TheDany4545/Tesis-2022-Erick-Aquino/Estimulador/Caracterizacion/Gráficas/frec_rampa_20.png

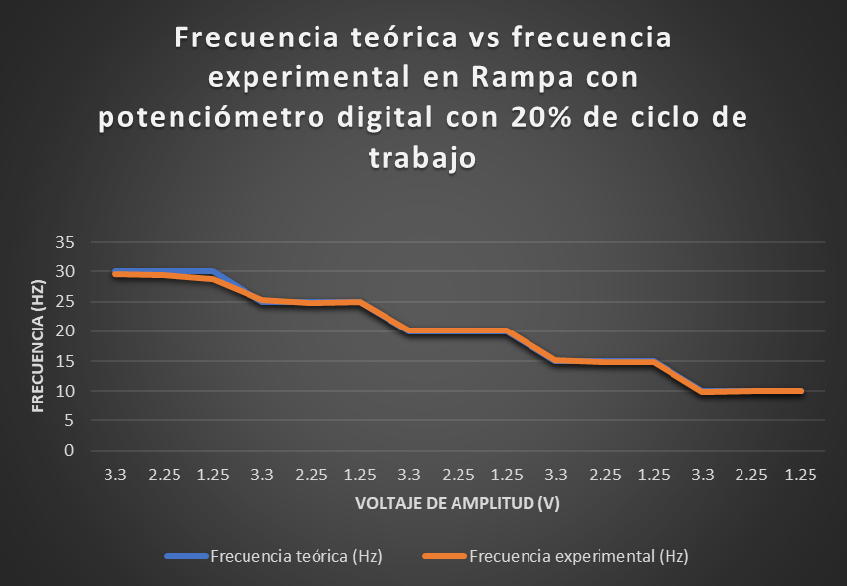
Estimulador/Caracterizacion/Gráficas/frec_rampa_20.png
