TheDany4545/Tesis-2022-Erick-Aquino/Documentación/Scheamtics/trinketM0_2.jpg

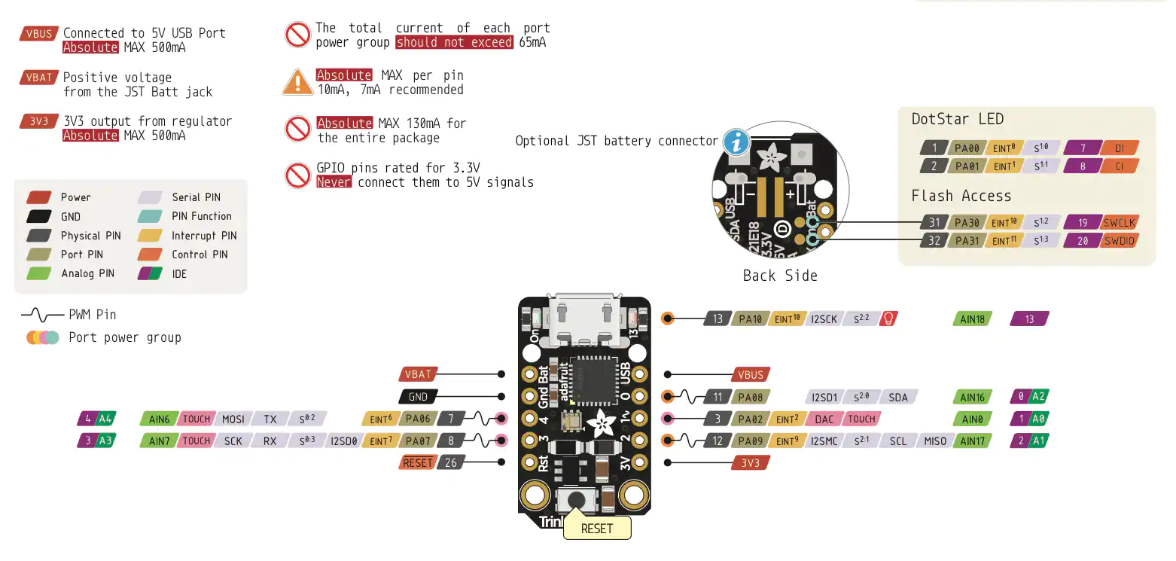
Documentación/Scheamtics/trinketM0_2.jpg
