TheDany4545/Tesis-2022-Erick-Aquino/Documentación/Esquemas_Fritzing/Emulador_ECG/Raspi4_to_TTL.PNG

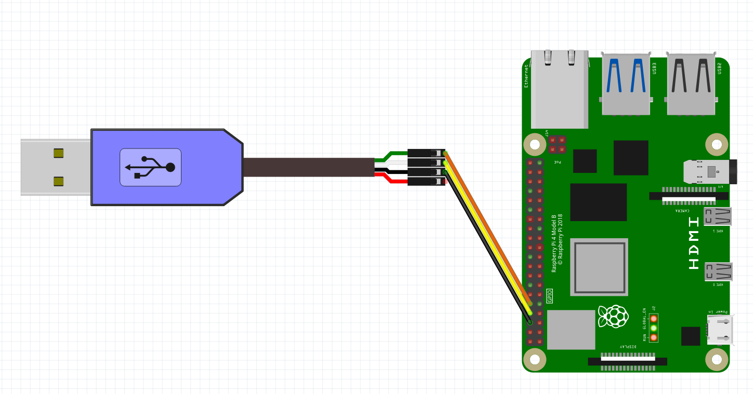
Documentación/Esquemas_Fritzing/Emulador_ECG/Raspi4_to_TTL.PNG
