TheDany4545/Tesis-2022-Erick-Aquino/Documentación/Esquemas_Fritzing/Estimulador_Parte_inalambrica/Estimulador Parte Inalambrica.PNG

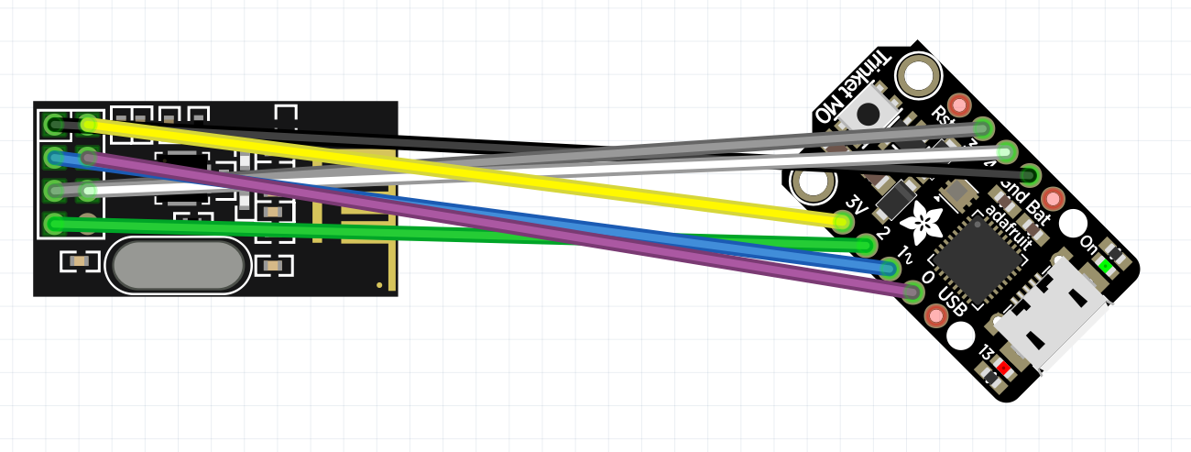
Documentación/Esquemas_Fritzing/Estimulador_Parte_inalambrica/Estimulador Parte Inalambrica.PNG
