TheDany4545/Tesis-2022-Erick-Aquino/Documentación/Esquemas_Fritzing/Varilla_Programadora/Varilla_programadora.PNG

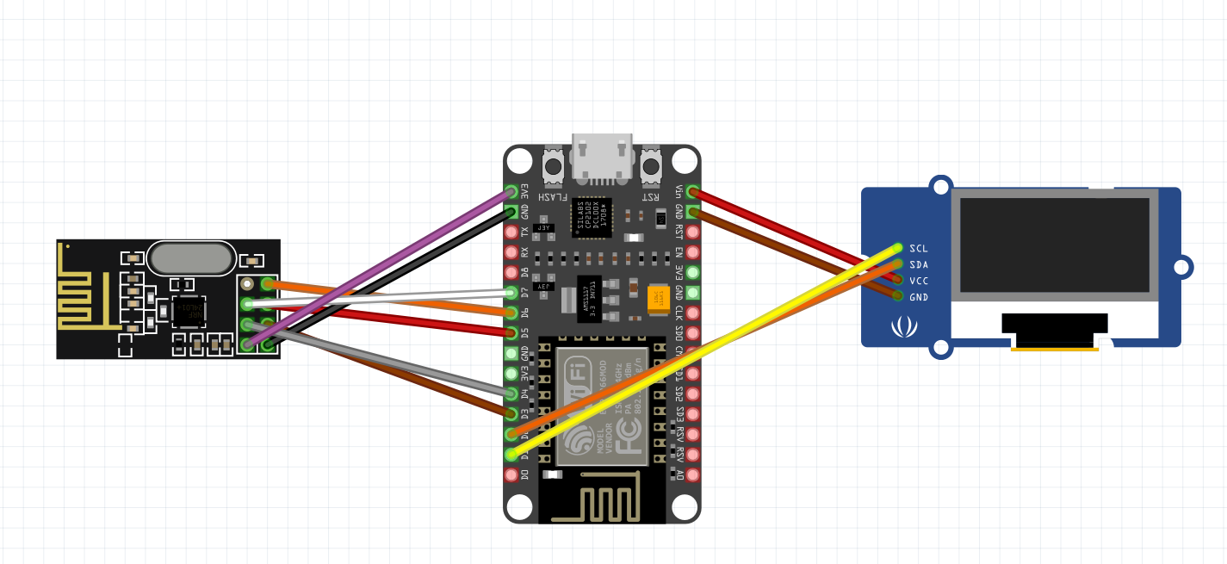
Documentación/Esquemas_Fritzing/Varilla_Programadora/Varilla_programadora.PNG
