TheDany4545/Tesis-2022-Erick-Aquino/Estimulador/Caracterizacion/Gráficas/5hz_Pot_PWM_1_7vpng.png

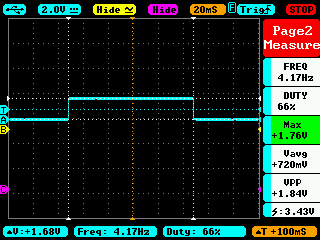
Estimulador/Caracterizacion/Gráficas/5hz_Pot_PWM_1_7vpng.png
