TheDany4545/Tesis-2022-Erick-Aquino/Estimulador/Caracterizacion/Gráficas/6hz_Pot_PWM_3_3v.png

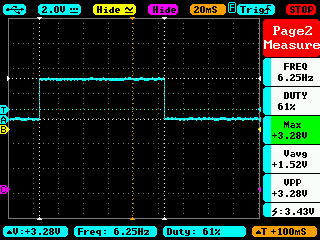
Estimulador/Caracterizacion/Gráficas/6hz_Pot_PWM_3_3v.png
