TheDany4545/Tesis-2022-Erick-Aquino/Estimulador/Caracterizacion/Gráficas/25hz_Pot_PWM_0_8vpng.png

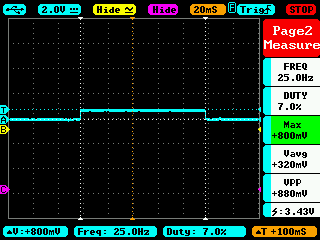
Estimulador/Caracterizacion/Gráficas/25hz_Pot_PWM_0_8vpng.png
