TheDany4545/Tesis-2022-Erick-Aquino/Estimulador/Caracterizacion/Gráficas/amplitud_rampa_20dt.png

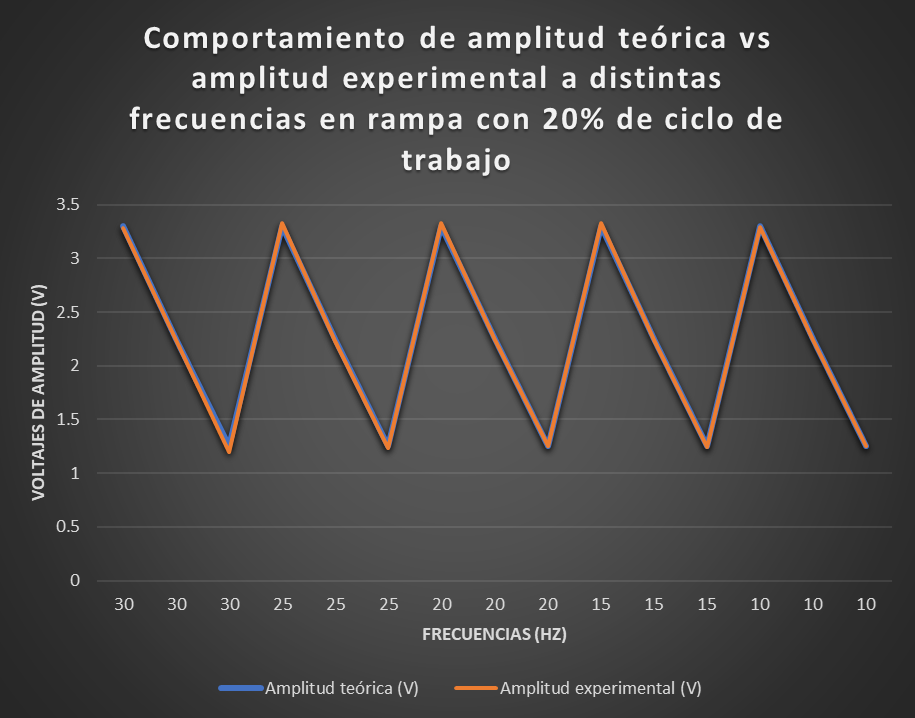
Estimulador/Caracterizacion/Gráficas/amplitud_rampa_20dt.png
