TheDany4545/Tesis-2022-Erick-Aquino/Estimulador/Caracterizacion/Rampa/10hz/10hz_50_duty_1.25v_completa.BMP

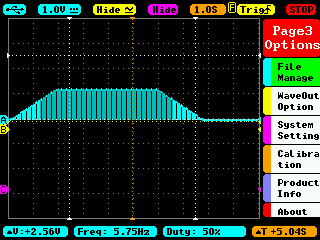
Estimulador/Caracterizacion/Rampa/10hz/10hz_50_duty_1.25v_completa.BMP
