TheDany4545/Tesis-2022-Erick-Aquino/Estimulador/Caracterizacion/Rampa/10hz/10hz_55_duty_3.3v_bajada.BMP

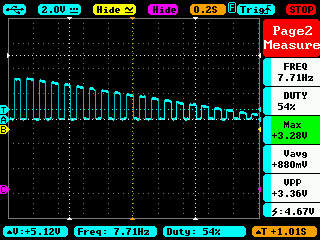
Estimulador/Caracterizacion/Rampa/10hz/10hz_55_duty_3.3v_bajada.BMP
