TheDany4545/Tesis-2022-Erick-Aquino/Estimulador/Caracterizacion/Rampa/20 hz/IMG_016.BMP

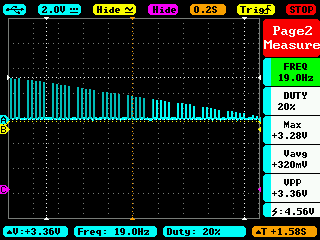
Estimulador/Caracterizacion/Rampa/20 hz/IMG_016.BMP
