TheDany4545/Tesis-2022-Erick-Aquino/Estimulador/Caracterizacion/Rampa/20 hz/IMG_018.BMP

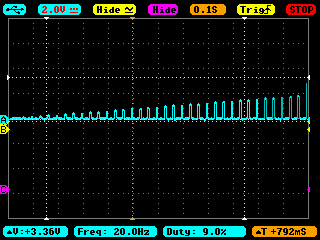
Estimulador/Caracterizacion/Rampa/20 hz/IMG_018.BMP
