TheDany4545/Tesis-2022-Erick-Aquino/Estimulador/Caracterizacion/Rampa/25hz/25hz_55 duty_1.25v.BMP

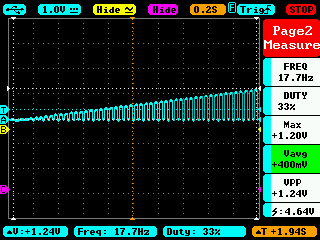
Estimulador/Caracterizacion/Rampa/25hz/25hz_55 duty_1.25v.BMP
