TheDany4545/Tesis-2022-Erick-Aquino/Estimulador/Caracterizacion/Rampa/25hz/25hz_55duty_3.3v.BMP

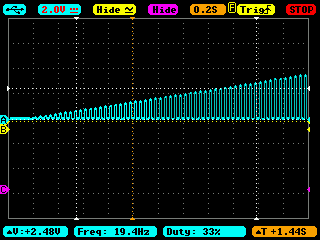
Estimulador/Caracterizacion/Rampa/25hz/25hz_55duty_3.3v.BMP
