TheDany4545/Tesis-2022-Erick-Aquino/Estimulador/Caracterizacion/Rampa/25hz/IMG_014.BMP

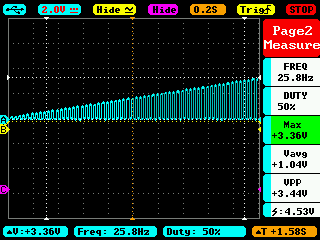
Estimulador/Caracterizacion/Rampa/25hz/IMG_014.BMP
