TheDany4545/Tesis-2022-Erick-Aquino/Estimulador/Caracterizacion/Rampa/30hz/30hz_20duty.BMP

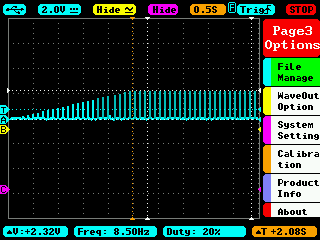
Estimulador/Caracterizacion/Rampa/30hz/30hz_20duty.BMP
