TheDany4545/Tesis-2022-Erick-Aquino/Estimulador/Caracterizacion/Rampa/30hz/30hz_20duty_bajada.BMP

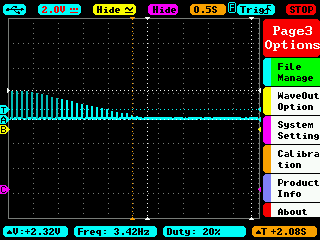
Estimulador/Caracterizacion/Rampa/30hz/30hz_20duty_bajada.BMP
