TheDany4545/Tesis-2022-Erick-Aquino/Estimulador/Caracterizacion/Rampa/30hz/IMG_012.BMP

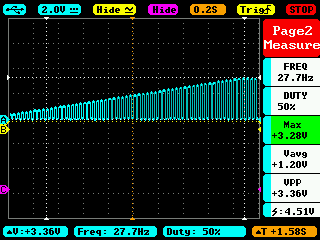
Estimulador/Caracterizacion/Rampa/30hz/IMG_012.BMP
