TheDany4545/Tesis-2022-Erick-Aquino/Varilla Programadora/Códigos_modo_automático/ECG/20s/resultados_sin_d.csv

Nombre | SD1 | SD2 | Position | target
data | 13.31929533 | 46.86123192 | 410.6818182 | 0
data2 | 15.47164829 | 39.13306395 | 400.9130435 | 0
data3 | 11.49636126 | 27.84833853 | 393.3478261 | 0
data4 | 9.135816219 | 11.72366131 | 389.6666667 | 0
data5 | 6.780729947 | 8.924402797 | 366.36 | 0
data6 | 11.19432558 | 26.71063552 | 413.8181818 | 0
data7 | 7.323431782 | 30.23123282 | 413.0909091 | 0
data8 | 9.179737126 | 32.68214266 | 405.6818182 | 0
data9 | 10.52865385 | 47.41748379 | 386.7083333 | 0
data10 | 8.855122497 | 26.75811144 | 365.68 | 0
data11 | 10.52865385 | 47.41748379 | 386.7083333 | 0
data12 | 11.22593846 | 21.22364676 | 399.3478261 | 0
data13 | 9.86276341 | 22.66189393 | 389.125 | 0
data14 | 9.81972929 | 36.98024059 | 377.96 | 0
data15 | 10.26191104 | 27.7152172 | 399.3043478 | 0
data16 | 10.62320818 | 36.60242123 | 396.125 | 0
data17 | 33.21924079 | 96.7259395 | 408.5454545 | 0
data18 | 15.4804312 | 68.95232955 | 428.8571429 | 0
data19 | 21.14951733 | 22.84549554 | 382.96 | 0
data20 | 9.992627668 | 22.32399033 | 412.4090909 | 0
run | 3.879716264 | 16.46211683 | 277.0560748 | 1
run2 | 77.89170851 | 90.03902385 | 176.922619 | 1
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
