TheDany4545/Tesis-2022-Erick-Aquino/Varilla Programadora/Códigos_modo_automático/Python_ECG/Leer_datos_y_ECG.py

################################# Librerias ##################################
import pandas as pd
import csv
import serial
import matplotlib.pyplot as plt
import scipy.signal
import funcion_BPK as fn
import pyhrv
import pyhrv.nonlinear as nl
import pyhrv.tools as tools
import numpy as np
import biosppy
import nolds
import spectrum
import sklearn as sk
from sklearn.model_selection import train_test_split
from sklearn.linear_model import LogisticRegression
from sklearn.metrics import accuracy_score
import random
############################ Código | Parte serial ############################
#Lugar de destino para guardar los datos recibidos
path_save = r'C:\Users\Daniel\Desktop\dato_leido.csv' 
ser = serial.Serial(
        port= ('COM7'),
        baudrate = 115200,
        parity=serial.PARITY_NONE,
        stopbits=serial.STOPBITS_ONE,
        bytesize=serial.EIGHTBITS,
        timeout=1
)
counter = 0
#Se borra lo que exista en el archivo
with open(path_save,'w') as f:
    pass
#Empiezo a leer los datos de la comunicacion serial, mientras no se envie nada
#hay un tiempo de espera, si no se envia nada durante esos segundos se cierra
#la comunicación serial 
#Si hay lectura de datos se guardan en un csv
while 1:
    read_line = ser.readline()
    decoded_line = read_line.decode('utf-8').rstrip()
    if decoded_line ==  "":
        print('No hay datos de entrada: ' + str(counter))
        counter = counter +1
        if counter == 20:
            print('Se cerró la comunicación serial')
            break
    else:         
        print(decoded_line)
        with open(path_save,"a") as file:
            file.write(decoded_line + "\n")
        counter = 0
    #print(decoded_line)
    
ser.close()
############################ Código | Parte ECG Análisis#######################


############################## Importing DATA ################################

column_names = ['time','ecg']

path = path_save
# path = r'Z:\Universidad UVG\Sexto Año\Segundo Ciclo\Tesis\Tesis-2022-Erick-Aquino\Programacion\Python_ECG\data.csv'



heart_data = pd.read_csv(path,names = column_names) # lee csv
#heart_data = heart_data.drop([0,1],axis =0) #Elimina encabezados default de Physiobank
heart_data['time'] = heart_data['time'].str.replace("'","") # Remove quotes 
heart_data['time'] = heart_data['time'].str.replace(":"," ") #add space
heart_data['time'] = heart_data['time'].str.replace("."," ",regex = False) #add space
######################### Funcion formato de tiempo a Segundos###############
def to_seconds(hora):
    mins, segs, ms, = hora.split(" ")
    #return int(mins)*360 + int(segs) + float(ms)
    return int(segs)+float (ms)/1000

######################### Columna time en segundos###########################
heart_data['time'] = heart_data['time'].map(to_seconds)
print(heart_data)

############################# Filtro butterworth #############################

Wn = 0.2 #Cut out frequencies higher 50 hZ
b, a = scipy.signal.butter(4,Wn, 'low', analog = False) #filtro orden 4
heart_data_filtered = scipy.signal.filtfilt(b,a,heart_data.ecg)

################################# Graficas ##################################
plt.plot(heart_data.time, heart_data.ecg)
plt.plot(heart_data.time, heart_data_filtered)
#plt.show(()
############################# Posicion picos ################################

picos,_ = scipy.signal.find_peaks(heart_data_filtered,height=(0.4))
plt.plot(heart_data.time, heart_data_filtered)
plt.plot(heart_data.time[picos], heart_data_filtered[picos],"X")
plt.show()
############################ better peak finder #############################

# Function that looks the peaks on the derivative
d_ecg, peaks_d_ecg = fn.decg_peaks(heart_data_filtered, heart_data.time)
plt.show()

#Function with other parameters as height and x distance
#Corrige los picos
Rwave_peaks_d_ecg = fn.d_ecg_peaks(d_ecg,peaks_d_ecg,heart_data.time,0.59,0.3)
plt.show()

#Grafica donde vemos la derivada y la original, pero comparando los picos de 
#ambas graficas y poniendo el pico de la derivada en la original, esto para
#descaratar falsos picos en la lectura del ECG
Rwave_t = fn.Rwave_peaks(heart_data_filtered, d_ecg, Rwave_peaks_d_ecg,heart_data.time)
plt.show()
################################ RR interval ###############################
#comparamos un data point de un pico con el otro datapoint del siguiente pico
RR_intervalo = 1/2*np.diff(Rwave_t)



#Load Sample Data
#signal = np.loadtxt(r'C:\Users\Daniel\Desktop\SampleECG.txt')[:,-1]

#Usando biosppy para los R peaks
#t,_,rpeaks = biosppy.signals.ecg.ecg(signal)[:3]
#t, filtered_signal, rpeaks = biosppy.signals.ecg.ecg(signal)[:3]

#Poincare compute
#results = pyhrv.nonlinear.poincare(rpeaks=t[rpeaks])

#nni = tools.nn_intervals(t[rpeaks])

#poincare plot
#figure()
#result = nl.poincare(nni)#,ellipse=True,vectors=True, legend = True)
nni_results = nl.poincare(RR_intervalo, ellipse= True, vectors= True, legend= True)

# SD1 (T) REFLEJA LA VARIACIÓN DE LATIDO A LATIDO / Variabilidad latido a latido
SD1 = nni_results['sd1']
# SD2 (L) RELFLEJA LAS FLUCTUACIONES GENERALES / Variabilidad en el tiempo
SD2 = nni_results['sd2']
centro = nni_results['centro']

print('SD1 es:',SD1)
print('SD2 es:',SD2)
print('Centro es: ',centro)


##############################################################################
############################ MACHINE LEARNING ################################

path_MC = r'C:\Users\Daniel\Desktop\ECG\resultados_Nueva_data.csv'

rand = random.randint(1, 300)
print('El valor aleatorio es: ', rand )
resultados = pd.read_csv(path_MC)
results = resultados.drop(columns='Nombre',axis=1)
x = results.drop(columns='target',axis=1) #Me quedo con mis features
x = x.values
y = results['target'] # Me quedo con las salidas
y = y.values

x_train, x_test, y_train, y_test = train_test_split(x, y,
                                                    test_size = 0.5,
                                                    stratify=y,
                                                    random_state= rand )
print(x.shape, x_train.shape, x_test.shape)

model = LogisticRegression()
model.fit(x_train, y_train)

#Precision en training data
x_train_prediction = model.predict(x_train)
training_data_accuracy = accuracy_score(x_train_prediction, y_train)
print('Accuracy of the Training data:', training_data_accuracy)

x_test_prediction = model.predict(x_test)
test_data_accuracy = accuracy_score(x_test_prediction, y_test)
print('Accuracy of the Test data:', test_data_accuracy)

################### INPUT #########################
#input_data = (13.58965485243332,26.504190375071182,404.5652173913044) # Resposo Data P31
#input_data = (24.64204884,28.66216291,254.7130435) #ejercicio bike 5 60 segs
#input_data = (28.112780899538947,60.21766990988758,315.0752688172043) #ejercicio MIT 322 60 segs
#input_data = (180.46866958812709,174.00529805152485,380.57142857142856) #ejercicio MIT 323 60 segs
input_data = (SD1,SD2,centro) #ejercicio MIT 325 60 segs


#cambiando un poco to numpy array
input_data_as_numpy_array = np.asarray(input_data)

#reshape the numpy array as we are predicting for only one instance
input_data_reshape = input_data_as_numpy_array.reshape(1,-1)

prediction = model.predict(input_data_reshape)
print(prediction)
if (prediction[0]==0):
  print('La persona esta en reposo según su ECG')
else:
  print('La persona esta haciedo un esfuerzo físico según su ECG')
